CyberPit/FreeDSP-FreeDSP_SMD_AB/SIGMA STUDIO/Volume_TURU.GIF

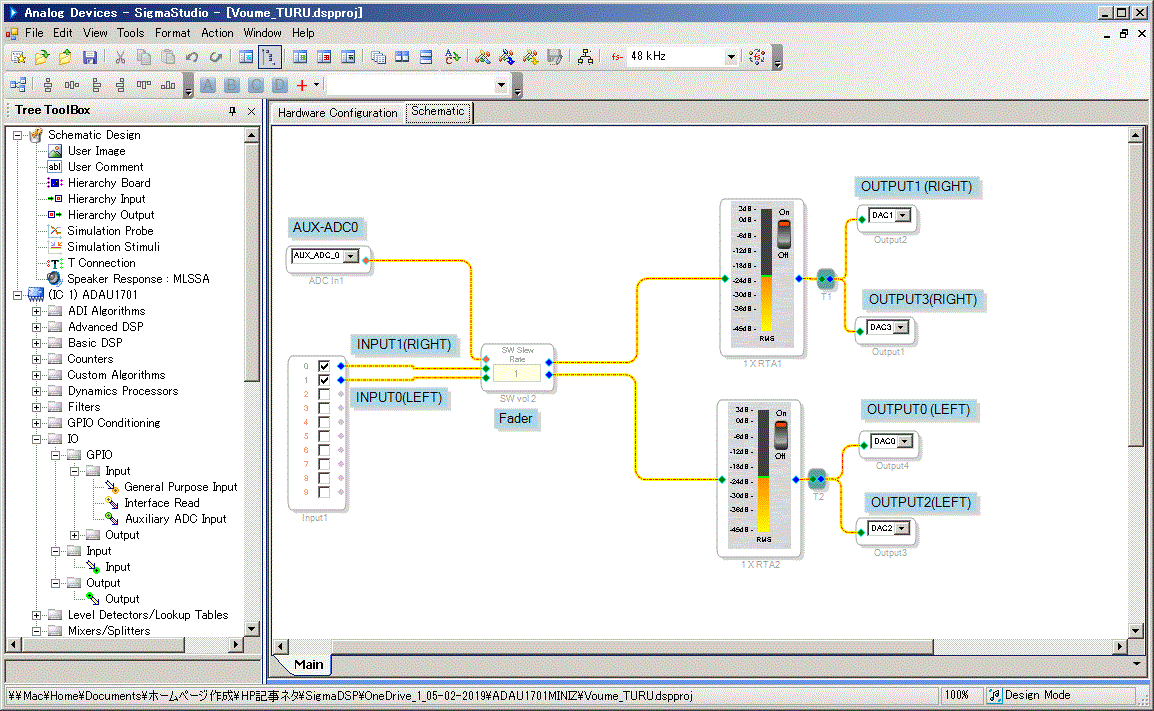
SIGMA STUDIO/Volume_TURU.GIF
