CyberPit/FreeDSP-FreeDSP_SMD_AB/Photo/biampinstallation.jpg

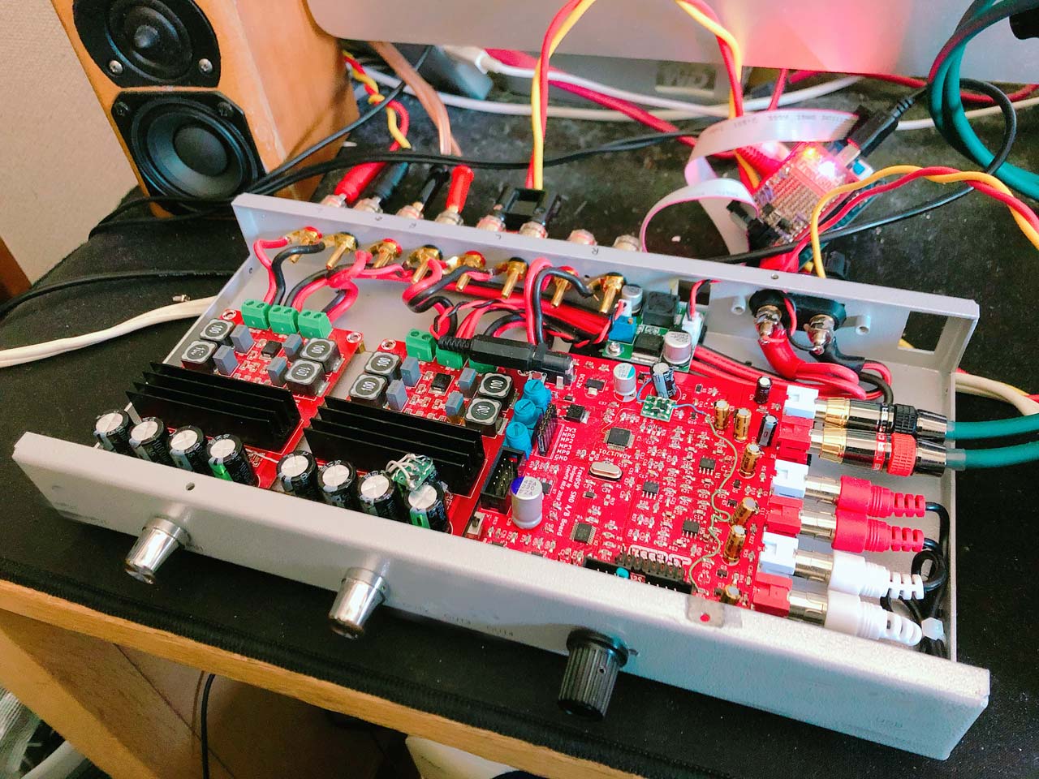
Photo/biampinstallation.jpg
